happybono/FinedustMonitorWithGPS/FinedustMonitorWithGPS/temperature.ino

//
//    FILE: temperature.ino
//  AUTHOR: Jaewoong Mun (happybono@outlook.com)
// CREATED: November 19, 2019
//
// Released to the public domain
//

#include <OneWire.h>
#include <DallasTemperature.h>

#define ONE_WIRE_BUS D4

OneWire oneWire(ONE_WIRE_BUS);
DallasTemperature DS18B20(&oneWire);

void setup_temperature() {
  DS18B20.begin();
}

float get_temperature() {
  float temp;
  do {
    DS18B20.requestTemperatures(); 
    temp = DS18B20.getTempCByIndex(0);
    delay(100);
  } while (temp == 85.0 || temp == (-127.0));
  return temp;
}
